usedhondacivic/ECE-4760-POV-Display/PYTHON/pov_images/bird/frame-00-delay-005s.bmp

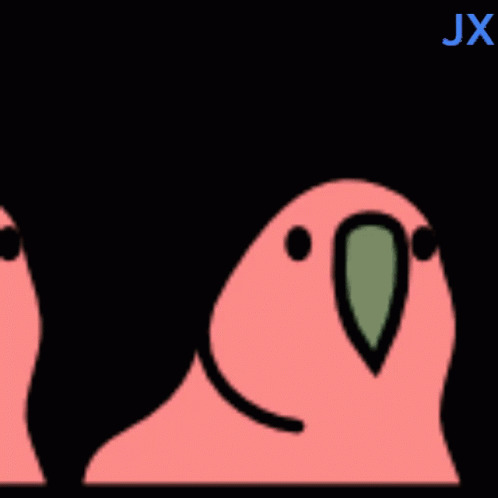
PYTHON/pov_images/bird/frame-00-delay-005s.bmp
