usedhondacivic/ECE-4760-POV-Display/PYTHON/pov_images/bird/frame-03-delay-005s.bmp

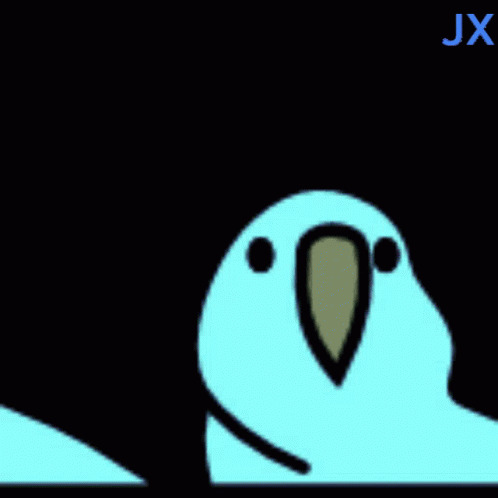
PYTHON/pov_images/bird/frame-03-delay-005s.bmp
