usedhondacivic/ECE-4760-POV-Display/PYTHON/pov_images/bruce.bmp

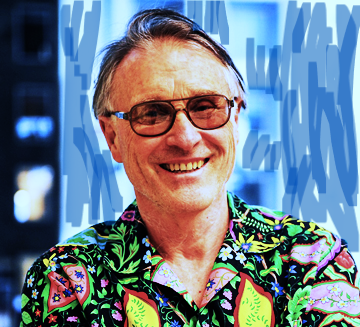
PYTHON/pov_images/bruce.bmp
