usedhondacivic/ECE-4760-POV-Display/PYTHON/pov_images/color_wheel.bmp

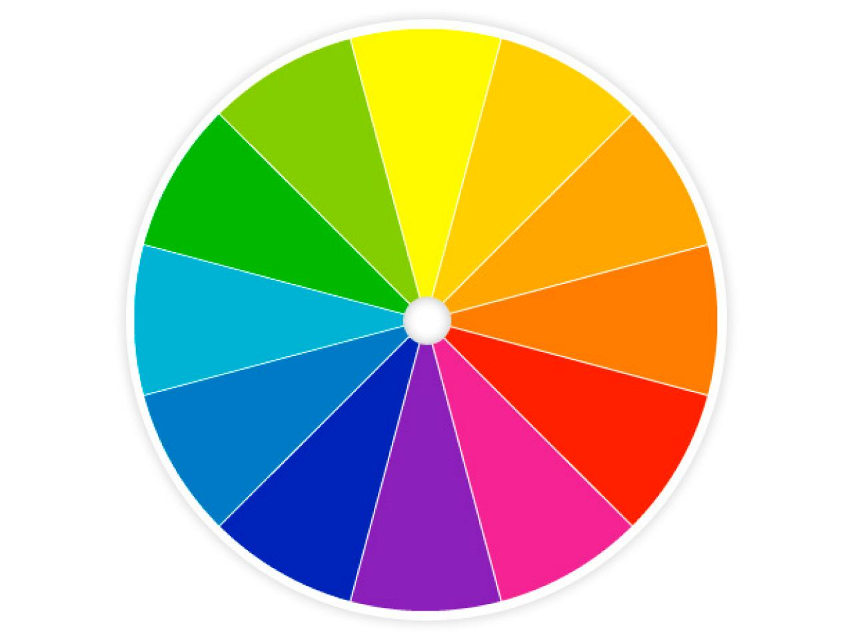
PYTHON/pov_images/color_wheel.bmp
