usedhondacivic/ECE-4760-POV-Display/PYTHON/pov_images/flower/4.bmp

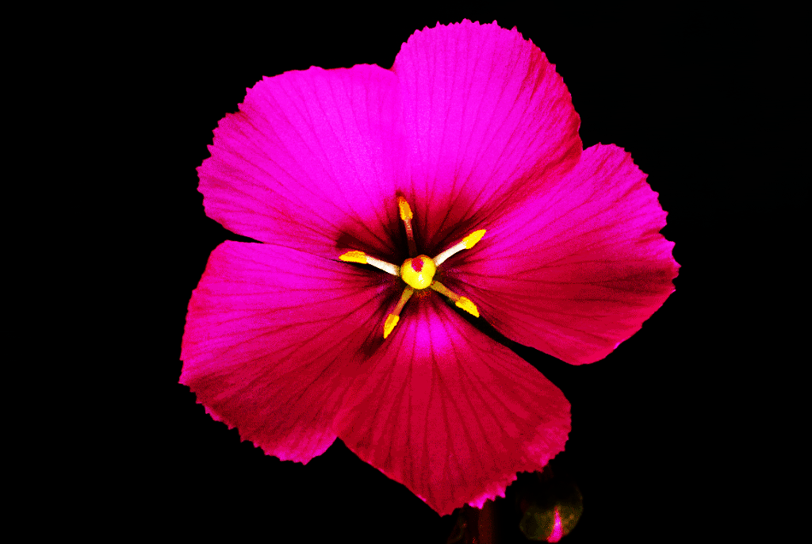
PYTHON/pov_images/flower/4.bmp
