usedhondacivic/ECE-4760-POV-Display/PYTHON/pov_images/flower/original/frame_3_delay-0.2s.gif

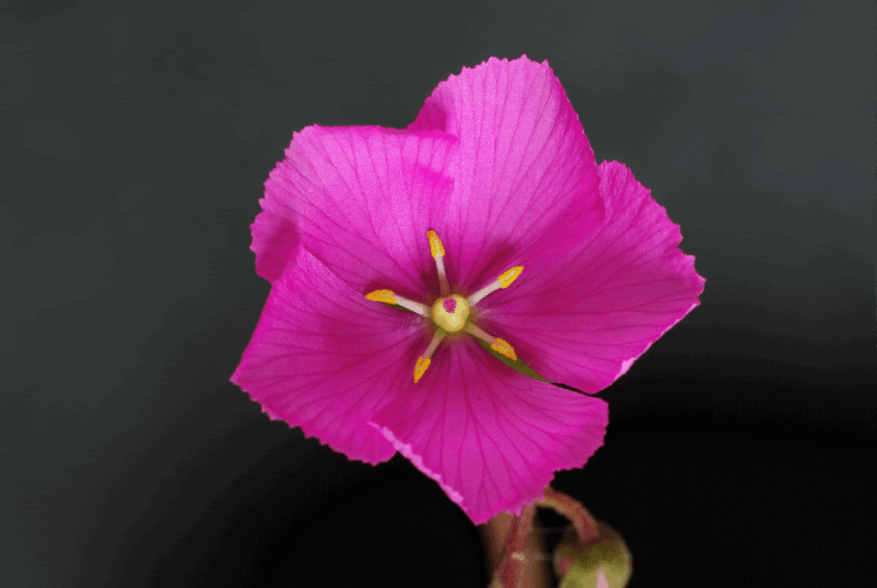
PYTHON/pov_images/flower/original/frame_3_delay-0.2s.gif
