usedhondacivic/ECE-4760-POV-Display/PYTHON/pov_images/flower/original/frame_5_delay-0.2s.gif

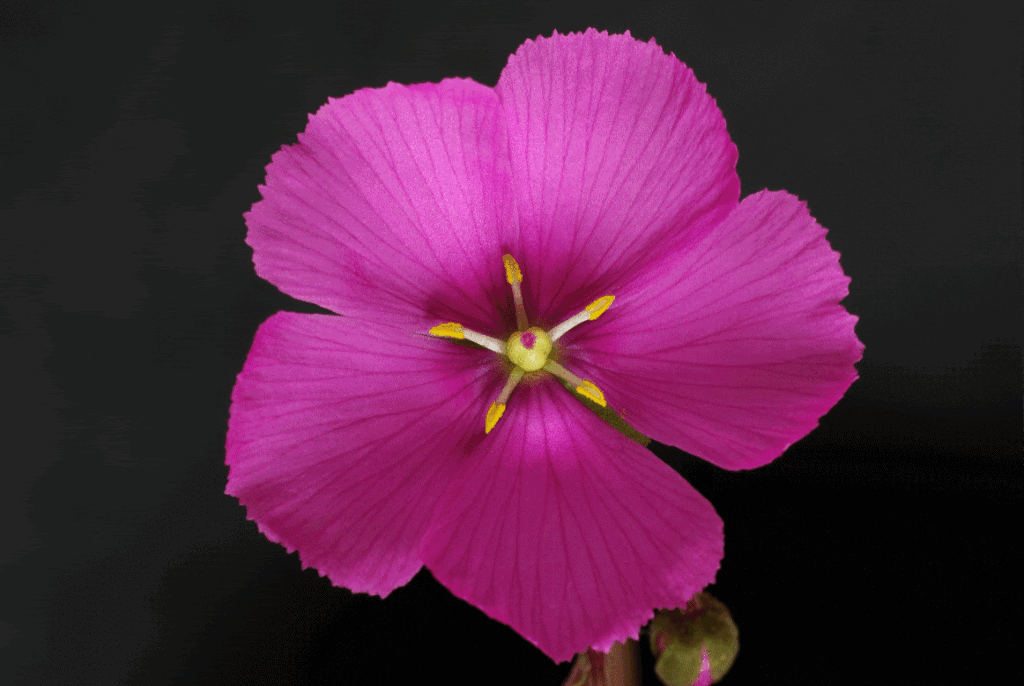
PYTHON/pov_images/flower/original/frame_5_delay-0.2s.gif
