usedhondacivic/ECE-4760-POV-Display/PYTHON/pov_images/globe.bmp

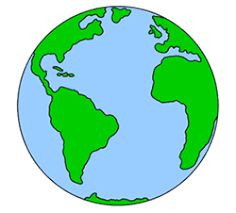
PYTHON/pov_images/globe.bmp
