usedhondacivic/ECE-4760-POV-Display/PYTHON/pov_images/hunter.bmp

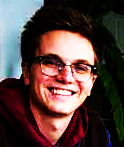
PYTHON/pov_images/hunter.bmp
