usedhondacivic/ECE-4760-POV-Display/PYTHON/pov_images/red.bmp

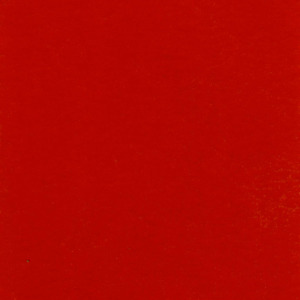
PYTHON/pov_images/red.bmp
