usedhondacivic/ECE-4760-POV-Display/PYTHON/pov_images/spiral.bmp

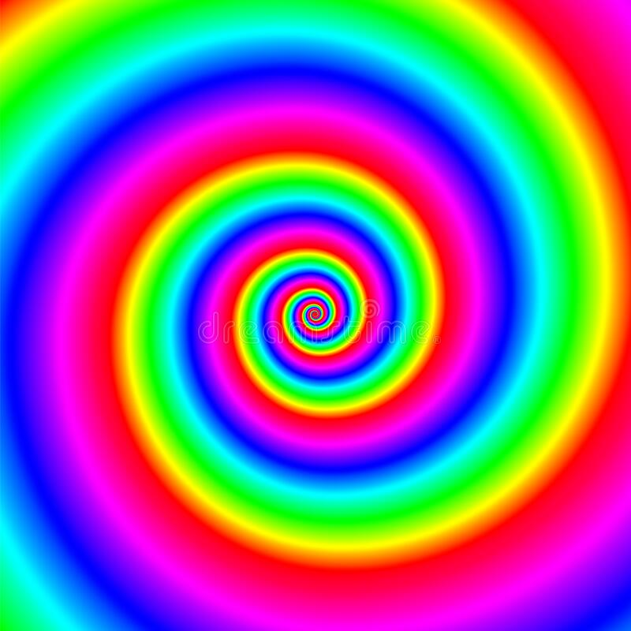
PYTHON/pov_images/spiral.bmp
